maanavkoladia/DigiPiano/resources/src/img/kicad_adding_libraries/3.png

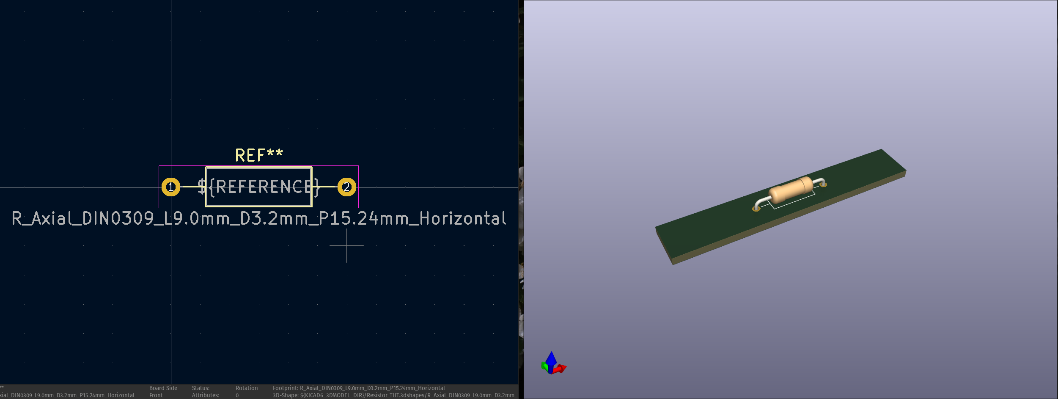
resources/src/img/kicad_adding_libraries/3.png
