maanavkoladia/DigiPiano/sw/KeyReader/inc/Unified_Port_Init.c

// ---------------------------------------------------------------------------
//
// File name:     Unified_Port_Init.c
// 
// Author:        Mark McDermott
// Orig gen date: July 12, 2020
// Last update:   September 12, 2020   Fix references to SSI3
// 
// Description:   This is the unified Port initialization routine for 
//                the 2020 Labs
//
// Usage:         Call Unified_Port_Init() if you want to initialize all ports (preferred)
//                Call the individual port inits as needed.
//
// ---------------------------------------------------------------------------


#include "tm4c123gh6pm.h"
#include "Unified_Port_Init.h"
#include "stdint.h"

// ---------------------------    Port_Init     ------------------------------

void Unified_Port_Init(void){
  Port_A_Init();
  Port_B_Init();  
  Port_C_Init();
  Port_D_Init();
  Port_E_Init();  
  Port_F_Init();
}

// ----------------------------------------------------------------------------
// ----------------    PORT A Initialization   --------------------------------
// ----------------------------------------------------------------------------
//
// Port A drives the ST7735 LCD 
//
// Backlight (pin 10) connected to +3.3 V
// MISO      (pin 9)  connected to PA4
// SCK       (pin 8)  connected to PA2 (SSI0Clk)
// MOSI      (pin 7)  connected to PA5 (SSI0Tx)
// TFT_CS    (pin 6)  connected to PA3 (SSI0Fss)
// CARD_CS   (pin 5)  connected to PB0 (GPIO)
// Data/CMD  (pin 4)  connected to PA6 (GPIO), high for data, low for command
// RESET     (pin 3)  connected to PA7 (GPIO)
// VCC       (pin 2)  connected to +3.3 V
// Gnd       (pin 1)  connected to ground
//
void Port_A_Init(void){ 
  
  SYSCTL_RCGCSSI_R      |= 0x01;            // Activate SSI0
  
  SYSCTL_RCGCGPIO_R     |= 0x01;            // Activate port A
  while((SYSCTL_PRGPIO_R & 0x01)==0){};     // allow time for clock to start
    
  GPIO_PORTA_DIR_R      |= 0xC8;            // make PA3,6,7 out
  GPIO_PORTA_AFSEL_R    &= ~0xC8;           // disable alt funct on PA3,6,7
  GPIO_PORTA_DEN_R      |= 0xC8;            // enable digital I/O on PA3,6,7
  
  // configure PA3,6,7 as GPIO
  GPIO_PORTA_PCTL_R      = (GPIO_PORTA_PCTL_R
                         & 0x00FF0FFF)
                         + 0x00000000;
  
  GPIO_PORTA_AMSEL_R    &= ~0xC8;           // disable analog functionality on PA3,6,7

  // initialize SSI0
  GPIO_PORTA_AFSEL_R    |= 0x2C;            // enable alt funct on PA2,3,5
  GPIO_PORTA_DEN_R      |= 0x2C;            // enable digital I/O on PA2,3,5
 
  // configure PA2,3,5 as SSI
  GPIO_PORTA_PCTL_R      = (GPIO_PORTA_PCTL_R
                         & 0xFF0F00FF)
                         + 0x00202200;
  
  GPIO_PORTA_AMSEL_R    &= ~0x2C;           // disable analog functionality on PA2,3,5
  SSI0_CR1_R            &= ~SSI_CR1_SSE;    // disable SSI
  SSI0_CR1_R            &= ~SSI_CR1_MS;     // master mode
  
  // configure for system clock/PLL baud clock source
  SSI0_CC_R             = (SSI0_CC_R&~SSI_CC_CS_M)
                        + SSI_CC_CS_SYSPLL;
                                        
  // clock divider for 8 MHz SSIClk (80 MHz PLL/24)
  // SysClk/(CPSDVSR*(1+SCR))
  // 80/(10*(1+0)) = 8 MHz (slower than 4 MHz)
  SSI0_CPSR_R           = (SSI0_CPSR_R
                        &~SSI_CPSR_CPSDVSR_M)
                        + 10;               // must be even number
  
  // SCR = 0 (8 Mbps data rate)
  // SPH = 0
  // SPO = 0
  SSI0_CR0_R            &= ~(SSI_CR0_SCR_M           
                        | SSI_CR0_SPH             
                        | SSI_CR0_SPO);             
  
  // FRF = Freescale format
  SSI0_CR0_R            = (SSI0_CR0_R
                        &~SSI_CR0_FRF_M) 
                        + SSI_CR0_FRF_MOTO;
  
  // DSS = 8-bit data
  SSI0_CR0_R            = (SSI0_CR0_R
                        &~SSI_CR0_DSS_M)
                        + SSI_CR0_DSS_8;
  // enable SSI
  SSI0_CR1_R            |= SSI_CR1_SSE;              
  
}

// ----------------------------------------------------------------------------
// ----------------    PORT B Initialization   --------------------------------
// ----------------------------------------------------------------------------
//
// PB7 = PWM Ouptut to JP6 (M0PWM1)
// PB6 = PWM Output to Motor (M0PWM0)
// PB5 = ADC Input (AIN11)
// PB4 = Timer Capture input (T1CCP0)
// PB3 = GPIO 
// PB2 = GPIO/I2C0
// PB1 = GPIO/I2C0CL
// PB0 = ST7735 Card CS

void Port_B_Init(void){ 
  
  SYSCTL_RCGCPWM_R      |= 0x01;            // activate PWM0
  
  SYSCTL_RCGCGPIO_R     |= 0x02;            // activate port B
  while((SYSCTL_PRGPIO_R & 0x02) == 0){};   // Wait
  
  // ---------------  Initialize PB7 as M0PWM1  -----------------------  

  GPIO_PORTB_AFSEL_R    |=  0x80;           // enable alt funct on PB7
  GPIO_PORTB_PCTL_R     &= ~0xF0000000;     // configure PB7 as M0PWM1
  GPIO_PORTB_PCTL_R     |=  0x40000000;
  GPIO_PORTB_AMSEL_R    &= ~0x80;           // disable analog functionality on PB7
  GPIO_PORTB_DEN_R      |=  0x80;           // enable digital I/O on PB7

  // ---------------  Initialize PB6 as M0PWM0  -----------------------
  GPIO_PORTB_AFSEL_R    |=  0x40;           // enable alt funct on PB6
  GPIO_PORTB_PCTL_R     &= ~0x0F000000;     // configure PB6 as PWM0
  GPIO_PORTB_PCTL_R     |=  0x04000000;  
  GPIO_PORTB_AMSEL_R    &= ~0x40;           // disable analog functionality on PB6
  GPIO_PORTB_DEN_R      |=  0x40;           // enable digital I/O on PB6
  
  // ---------------  Initialize PB5 as AIN11  ----------------------- 
  GPIO_PORTB_DIR_R      &= ~0x20;           // make PB5 input
  GPIO_PORTB_AFSEL_R    |=  0x20;           // enable alternate function on PB5
  GPIO_PORTB_DEN_R      &= ~0x20;           // disable digital I/O on PB5
  GPIO_PORTB_AMSEL_R    |=  0x20;           // enable analog functionality on PB5

  // ----------------- Initialize PB4 as Timer Capture input (T1CCP0) ---------
  GPIO_PORTB_DIR_R      &= ~0x10;           // make PB4 input
  GPIO_PORTB_AFSEL_R    |= 0x10;            // enable alt funct on PB4
  GPIO_PORTB_DEN_R      |= 0x10;            // enable digital I/O on PB4
                                            // configure PB4 (T1CCP0)
  GPIO_PORTB_PCTL_R     = (GPIO_PORTB_PCTL_R 
                        &  0xFFF0FFFF)
                        +  0x00070000;
  GPIO_PORTB_AMSEL_R    &= ~0x10;           // disable analog functionality on PB4

  // ----------------- Initialize PB3-0 as GPIO ---------
                                      
  GPIO_PORTB_PCTL_R     &= ~0x0000FFFF;     // GPIO
  GPIO_PORTB_DIR_R      |=  0x0F;           // make PB3-0 out
  GPIO_PORTB_AFSEL_R    &= ~0x0F;           // regular port function
  GPIO_PORTB_DEN_R      |=  0x0F;           // enable digital I/O on PB3-0
  GPIO_PORTB_AMSEL_R    &= ~0x0F;           // disable analog functionality on PB3-0
  
  
  }
 
// ----------------------------------------------------------------------------
// ----------------    PORT C Initialization   --------------------------------
// ----------------------------------------------------------------------------
//
// PC4 = UP switch
// PC5 = RIGHT switch
// PC6 = LEFT switch
// PC7 = DOWN switch
//

void Port_C_Init(void){ 
  
  SYSCTL_RCGCGPIO_R     |=  0x04;         // Activate clock for Port C
  while((SYSCTL_PRGPIO_R & 0x04) != 0x04){};  // Allow time for clock to start
   
  GPIO_PORTC_PCTL_R     &= ~0xFFFF0000;   // regular GPIO
  GPIO_PORTC_AMSEL_R    &= ~0xF0;         // disable analog function 
  GPIO_PORTC_DIR_R      &= ~0xF0;         // inputs on PC7-PC4
  GPIO_PORTC_AFSEL_R    &= ~0xF0;         // regular port function
  GPIO_PORTC_PUR_R       =  0xF0;         // enable pull-up on PC7-PC4
  GPIO_PORTC_DEN_R      |=  0xF0;         // enable digital port 
  }  
  
// ----------------------------------------------------------------------------
// ----------------    PORT D Initialization   --------------------------------
// ----------------------------------------------------------------------------
//
// PD7 = U2TX
// PD6 = U2RX
// PD3 = SSI1_MOSI  (to TLV5616)
// PD2 = AIN5 (Monitor DAC_OUT signal from TLV5616)
// PD1 = SSI1_FS/CS (to TLV5616)
// PD0 = SSI1_SCK   (to TLV5616)
  
void Port_D_Init(void){
 
  SYSCTL_RCGCGPIO_R     |= 0x08;            // activate port D
  while((SYSCTL_PRGPIO_R & 0x08)==0){};     // allow time for clock to stabilize

  // ---------------  Initialize PB7 as U2TX, PB6 as U2RX  -----------------------  
    
  GPIO_PORTD_LOCK_R      = 0x4C4F434B;      // unlock REQUIRED for PD7
  GPIO_PORTD_CR_R       |= 0xC0;            // commit PD6, PD7
  
  GPIO_PORTD_AMSEL_R    &= ~0xC0;           // disable analog functionality on PD6, PD7
  GPIO_PORTD_AFSEL_R    |=  0xC0;           // enable alternate function on PD6, PD7
  GPIO_PORTD_DEN_R      |=  0xC0;           // enable digital on PD6, PD7 (PD6 is U2RX, PD7 is U2TX)
  GPIO_PORTD_PCTL_R      =(GPIO_PORTD_PCTL_R  
                         & 0x00FFFFFF)
                         | 0x11000000;      // configure PD6, PD7 as UART
 
   // ---------------  Initialize PD2 as AIN5  ----------------------------------  
   
  GPIO_PORTD_DIR_R      &= ~0x04;           // make PD2 input
  GPIO_PORTD_AFSEL_R    |=  0x04;           // enable alternate function on PD2
  GPIO_PORTD_DEN_R      &= ~0x04;           // disable digital I/O on PD2
  GPIO_PORTD_AMSEL_R    |=  0x04;           // enable analog functionality on PD2

  // ---------------  Initialize PD3,1,0 as SSI1 MOSI, FS & SCK  ---------------- 
    
  GPIO_PORTD_AMSEL_R    &= ~0x0B;           // disable analog functionality on PD
  GPIO_PORTD_AFSEL_R    |=  0x0B;           // enable alt funct on PD3,1,0
  GPIO_PORTD_DEN_R      |=  0x0B;           // enable digital I/O on PD3,1,0
  GPIO_PORTD_PCTL_R      = (GPIO_PORTD_PCTL_R
                          & 0xFFFF0F00)
                          + 0x00002022;
}

// ----------------------------------------------------------------------------
// ----------------    PORT E Initialization   --------------------------------
// ----------------------------------------------------------------------------
//
// PE5 = U5TX
// PE4 = U5RX
// PE3 = Heartbeat LED
// PE2 = AIN_1 (DAC_OUT Monitor)
// PE1 = RSTB_8266
// PE0 = 8266_ GPIO_2 

void Port_E_Init(void){

  SYSCTL_RCGCGPIO_R     |= 0x10;            // activate port E
  while((SYSCTL_PRGPIO_R & 0x10)==0){};

 // ---------------  Initialize PE5 as U5TX, PE4 as U5RX  -----------------------  

  GPIO_PORTE_AFSEL_R    |= 0x30;            // enable alt funct on PE5-4
  GPIO_PORTE_DEN_R      |= 0x30;            // enable digital I/O on PE5-4
                                            // configure PE5-4 as UART
  GPIO_PORTE_PCTL_R      = (GPIO_PORTE_PCTL_R
                         & 0xFF00FFFF)
                         + 0x00110000;
  GPIO_PORTE_AMSEL_R    &= ~0x30;           // disable analog functionality on PE

 // ---------------  Initialize PE3,1,0 as GPIO  ---------------------------------  

  GPIO_PORTE_DIR_R      |=  0x0A;           // output digital I/O on PE3,1
  GPIO_PORTE_DIR_R      &= ~0x01;           // input digital I/O on PE0
  GPIO_PORTE_AMSEL_R    &= ~0x0B;           // disable analog functionality on PE3,1,0
  GPIO_PORTE_AFSEL_R    &= ~0x0B;           // disable alt funct on PE3,1,0
  GPIO_PORTE_DEN_R      |=  0x0B;           // enable digital I/O on PE3,1,0
  
  GPIO_PORTE_PCTL_R      = (GPIO_PORTE_PCTL_R 
                         & 0xFFFF0F00);
  
// ---------------  Initialize PE2 as AIN1  ---------------------------------  
  
  GPIO_PORTE_DIR_R      &= ~0x04;           // make PE2 input
  GPIO_PORTE_AFSEL_R    |=  0x04;           // enable alternate function on PE2
  GPIO_PORTE_DEN_R      &= ~0x04;           // disable digital I/O on PE2
  GPIO_PORTE_AMSEL_R    |=  0x04;           // enable analog functionality on PE2
}
  
// ----------------------------------------------------------------------------
// ----------------    PORT F Initialization   --------------------------------
// ----------------------------------------------------------------------------
//

void Port_F_Init(void){
  
  SYSCTL_RCGCGPIO_R     |= 0x00000020;      // activate clock for Port F
  while((SYSCTL_PRGPIO_R & 0x20)==0){};     // allow time for clock to stabilize
    
  GPIO_PORTF_LOCK_R     = 0x4C4F434B;       // unlock GPIO Port F
  GPIO_PORTF_CR_R       = 0x1F;             // allow changes to PF4-0
  
  GPIO_PORTF_AMSEL_R    = 0x00;             // disable analog on PF
  GPIO_PORTF_PCTL_R     = 0x00000000;       // PCTL GPIO on PF4-0
  GPIO_PORTF_DIR_R      = 0x0E;             // PF4,PF0 in, PF3-1 out
  GPIO_PORTF_AFSEL_R    = 0x00;             // disable alt funct on PF7-0
  GPIO_PORTF_PUR_R      = 0x11;             // enable pull-up on PF0 and PF4
  GPIO_PORTF_DEN_R      = 0x1F;             // enable digital I/O on PF4-0
}
